Dualock/Controlador-de-corriente-y-temperatura-Hytek/Presentación de avance/B42629 - B50747- Presentacion.pdf

# Diseño e implementación de un controlador de corriente y temperatura para diodos láser de alta corriente

## Utilizando tecnología Hytek e interfaz de usuario

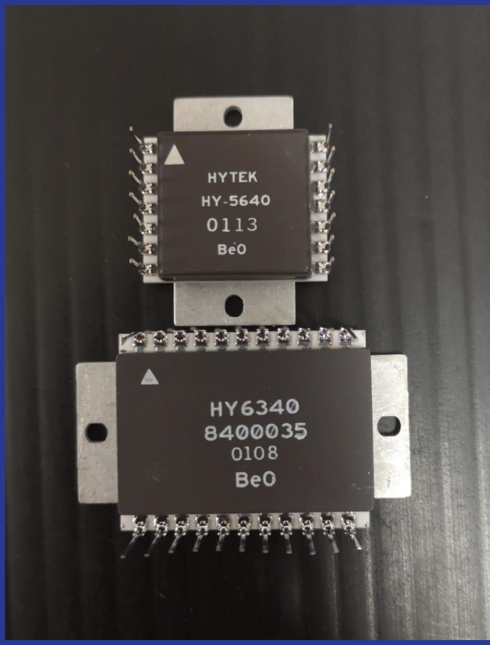
[picture p11: figure]

# Objetivo general

Diseñar e implementar un controlador de corriente y temperatura para diodos láser de alta corriente, utilizando controladores Hytek, un sistema embebido de bajo costo e interfaz de usuario

# Enfoque y metodología

Comprender el
funcionamiento de los
controladores

Desafío 2

Realizar un diseño
esquemático del circuito
de alimentación y las
configuraciones de los
controladores

Desafío 3

Conocer los modelos
correspondientes al TEC
y diodo laser

Desafío 1

# Enfoque y metodología

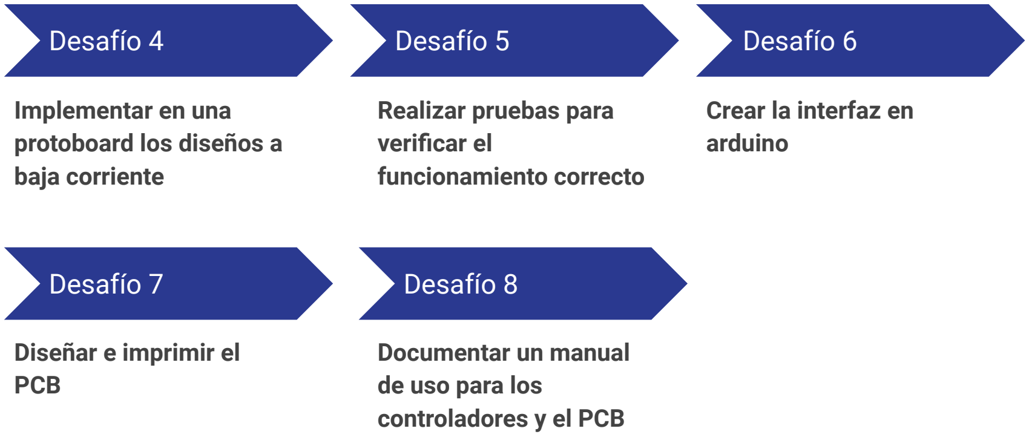
[picture p12: figure]
Implementar en una protoboard los diseños a baja corriente; Desafío 5; Realizar pruebas para verificar el funcionamiento correcto; Desafío 6; Documentar un manual de uso para los controladores y el PCB; Desafío 4; Desafío 7; Diseñar e imprimir el PCB; Desafío 8; Crear la interfaz en arduino
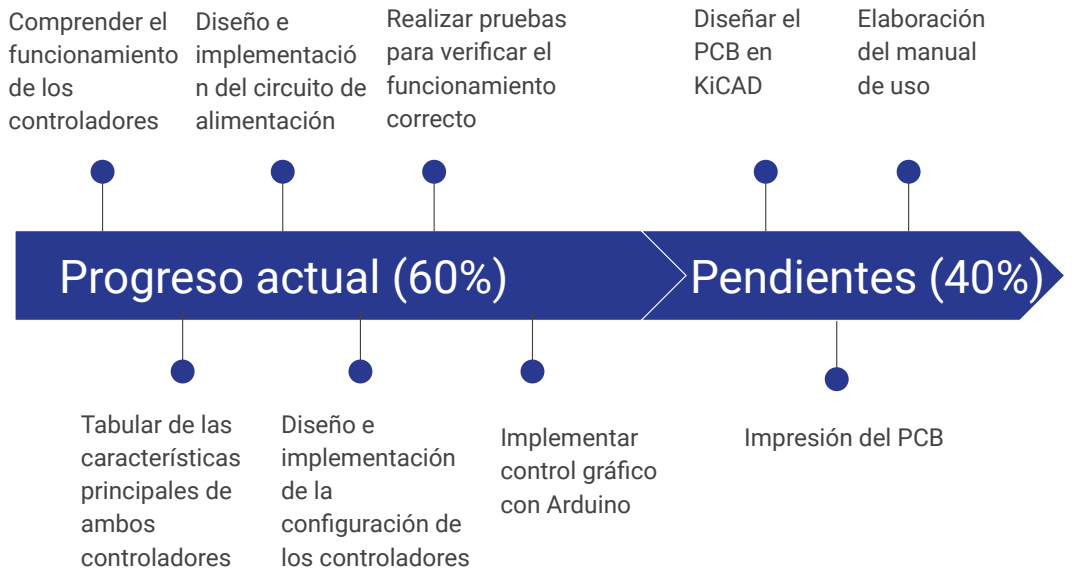
[picture p13: page 5]
Comprender el funcionamiento de los controladores; Elaboración del manual de uso; Progreso actual (60%); Pendientes (40%); Diseño e implementación de la configuración de los controladores; Implementar control gráfico con Arduino; Diseñar el PCB en KiCAD

Realizar pruebas
para verificar el
funcionamiento
correcto

Diseño e
implementació
n del circuito de
alimentación

Tabular de las
características
principales de
ambos
controladores

Impresión del PCB

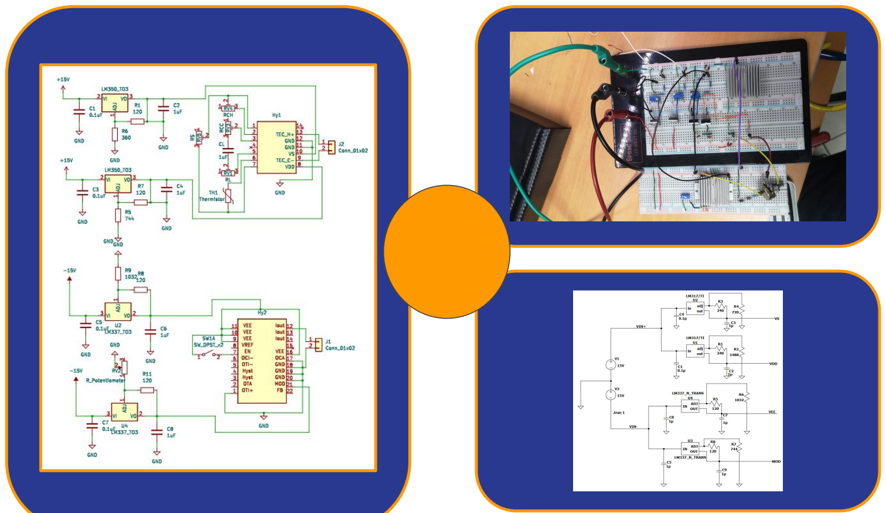
[picture p14: page 6]
