Dualock/Controlador-de-corriente-y-temperatura-Hytek/Interfaz_Arduino/Figuras/IoutVsMOD.png

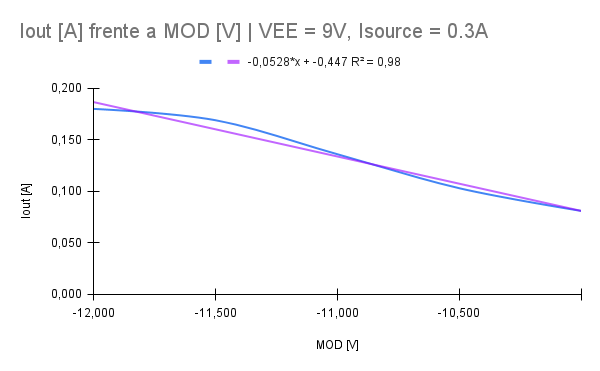
Interfaz_Arduino/Figuras/IoutVsMOD.png
