Dualock/Controlador-de-corriente-y-temperatura-Hytek/Simulacion del circuito de alimentacion LTSPice/Esquemático_circuito_de_alimentacion.pdf

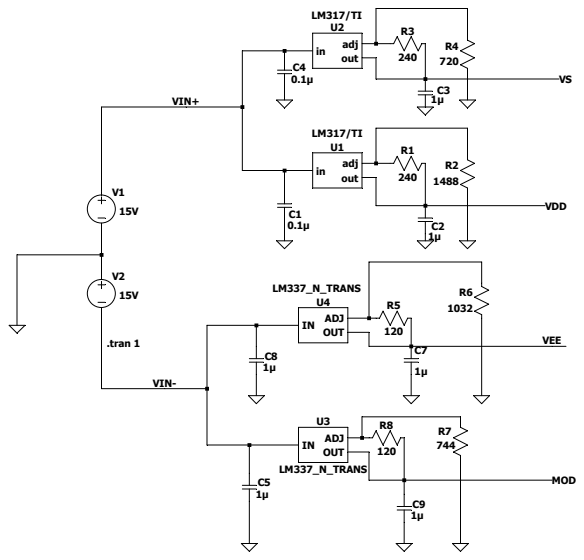
[picture p46: page 1]
