Dualock/Controlador-de-corriente-y-temperatura-Hytek/Simulacion del circuito de alimentacion LTSPice/Simulacion/Configuracion_Completa.asc

C1: cap; 0.1µ
C2: cap; 1µ
C3: cap; 1µ
C4: cap; 0.1µ
C5: cap; 1µ
C7: cap; 1µ
C8: cap; 1µ
C9: cap; 1µ
R1: res; 240
R2: res; 1488
R3: res; 240
R4: res; 720
R5: res; 120
R6: res; 1032
R7: res; 744
R8: res; 120
U1: LM317_TI
U2: LM317_TI
U3: LM337_N_TRANS
U4: LM337_N_TRANS
V1: voltage; 15V
V2: voltage; 15V
Named nets: 0, VS, MOD, VEE, VDD, VIN+, VIN-
.tran 1
